TommyE79/2d5/pictures/2d5_sensor_Platine_untere_Seite_2_SW_KONTRAST.png

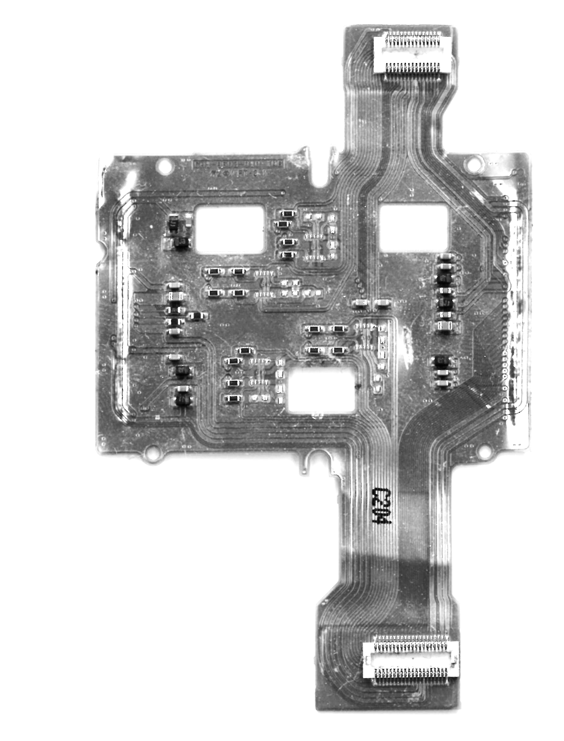
pictures/2d5_sensor_Platine_untere_Seite_2_SW_KONTRAST.png
