TommyE79/2d5/pictures/Sensor_Board_Messure_scale_top.jpg

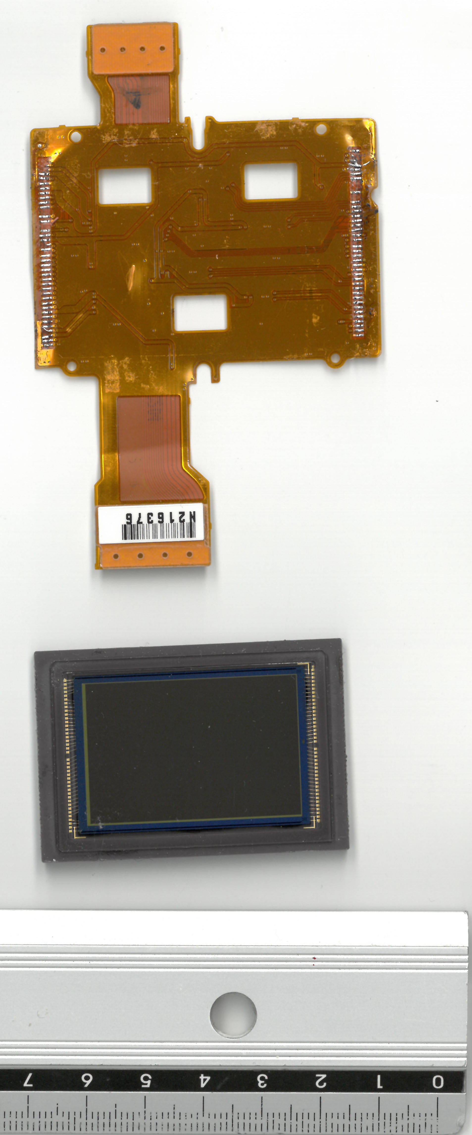
pictures/Sensor_Board_Messure_scale_top.jpg
