TommyE79/2d5/pictures/SKM_47_HIZO24041015270.tif

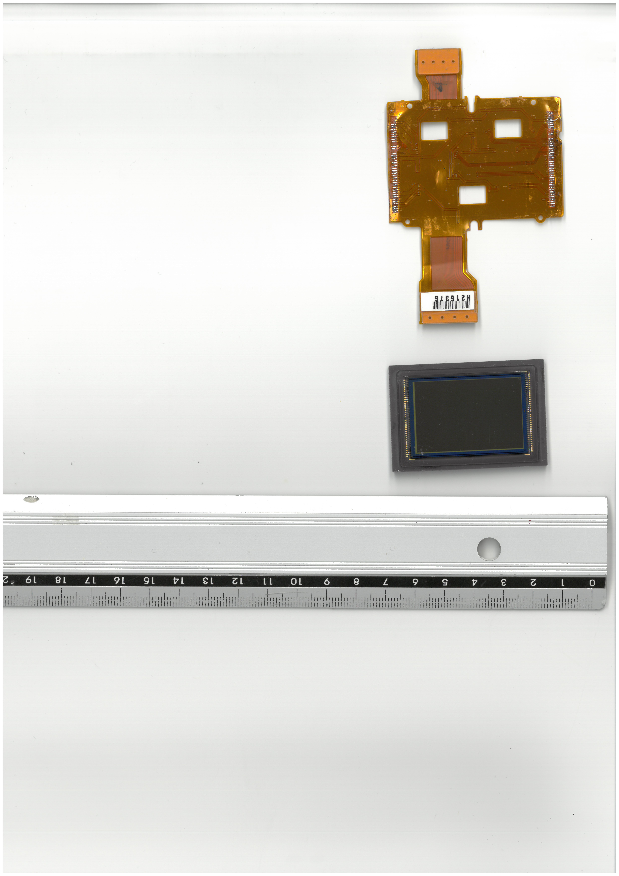
pictures/SKM_47_HIZO24041015270.tif
