TommyE79/2d5/sensor_board_back_engineered/sensor_board_back_engineered.kicad_pcb

## KiCad design Hardware/KiCAD/Computing_System.kicad_sch

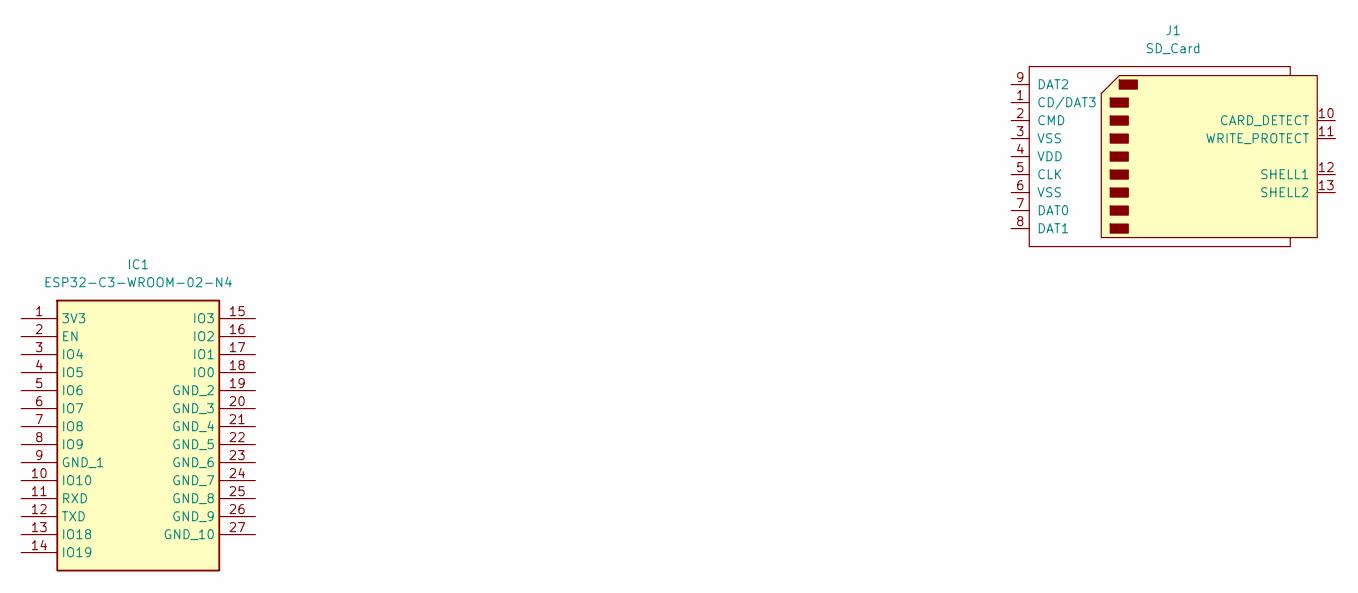
[picture p16: schematic Computing_System.kicad_sch]

Parts:
IC1: ESP32-C3-WROOM-02-N4; ESP32C3WROOM02N4; Manufacturer_Part_Number ESP32-C3-WROOM-02-N4; Mouser Part Number 356-ESP32C3WROOM02N4
J1: SD_Card
